averia/Orsini/software/MidiVox_Orsini/SynthEngine.ino

#include <avr/interrupt.h>
#include "SynthData.h"

// Oscillator internal variable

bool oscRunning = false;
float oscPosition = 0;
float oscSpeed = 0;
const prog_uint8_t *oscDataStart = 0;
int oscDataLen = 0;
int currentNote = 0;
float currentFrequency = 0;
float pitchBendVal = -12;
float freq = 261.6255653006f; //C3
fixed oscFCut = i2fp(1);
fixed oscFRes = 0;
fixed oscFMix = 0;
float oscLoopWidth = 1.0;
fixed ampValue=i2fp(1);
fixed fltHeight=0 ;
fixed fltSpeed=0 ;
fixed fltDelay=0 ;
fixed outValue=0 ; // output for release

// Oscillator external parameters
int oscShapeParam=0 ;
float oscFrequencyParam=0 ;

fixed clipFPlus=0 ;
fixed clipFMinus=0 ;

// Wave shape data
int oscShapeCount=6 ;

const prog_uint8_t *oscShapeTable[]= {
  sineTable,
  triTable,
  sawTable,
  squareTable,
  stairExpTable,
  particularHardTable,
};

#define DRIVER_SAMPLERATE 15625.0f

void SE_SetPitchBend(float pitchBend){                // EXPERIMENTAL
  pitchBendVal = pitchBend;
  if (oscFrequencyParam==0)  return;
  else{
    float freqFactor=(pow(2.0,(currentNote+pitchBendVal)/12.0)) ;
    currentFrequency = (freq*freqFactor);
    SE_SetFrequency(currentFrequency);
  }
};

void SE_SetFrequency(float frequency){
  if (frequency==0) {
    oscFrequencyParam=0 ;
    oscRunning=false ;
  }
  else {
    oscRunning=true ;
    oscFrequencyParam = frequency;
    oscSpeed=(frequency*oscDataLen)/DRIVER_SAMPLERATE; 
  }
};

void SE_SetNote(int note){
  currentNote=note;
  float freqFactor=(pow(2.0,(currentNote+pitchBendVal)/12.0)) ;
  //currentFrequency = freq*freqFactor;
  SE_SetFrequency(freq*freqFactor) ;
};

void updateLoopPoints() {
  // original squealer method
  //int len=oscShapeLength[oscShapeParam];
  //int o1=128;
  //int o2=0x100*oscLoopWidth ;
  //if (o1+o2>0x100) o2=0x100 ;

  oscDataStart=oscShapeTable[oscShapeParam];
  oscDataLen=0x100*oscLoopWidth;

  SE_SetFrequency(oscFrequencyParam) ;

}

void SE_SetShape(float shape) {
  int newShape=shape*oscShapeCount-0.01 ;
  if (newShape==oscShapeParam) return ;

  oscShapeParam=newShape ;
  updateLoopPoints() ;
  oscPosition=0;
};

void SE_SetWidth(float w) {
  oscLoopWidth=w;
  updateLoopPoints() ;                                  // DISABLED LOOP POINTS ... sorta
}

void SE_SetFilterCut(float cut) {
  oscFCut=fl2fp(cut*cut) ;
};

void SE_SetFilterMix(float mix) {
	
  oscFMix=fl2fp(mix) ;
};

void SE_SetOutput(float out) {
  outValue=fl2fp(out) ;
};

void SE_SetFilterRes(float res) {
  float tmpRes=(1-res) ;
  oscFRes=fl2fp(1-tmpRes*tmpRes*tmpRes) ;
};

void SynthEngine_Setup() {
  oscShapeParam=0 ;
  oscFrequencyParam=0 ;
  SE_SetNote(0) ;
  SE_SetShape(0.9) ;
  clipFPlus=i2fp(16-FIXED_SHIFT) ;
  clipFMinus=-clipFPlus ;
}

// variables for oscillators

uint16_t index = 0;          // index for wave lookup (the upper 8 bits of the accumulator)
fixed osc = 0;               // oscillator output
uint8_t rawOsc=0 ;

// ProcessSample:
// returns a unsigned 16 bit value
// to be sent to the DAC. This routine
// is called for every sample

uint16_t SynthEngine_ProcessSample() {

  // Return 0 if we don't run
  if (!oscRunning){
   return 0x8000 ;
  }
  // calculate new position inside the
  // current wavetable. 

  oscPosition +=oscSpeed ;  // add in pith, the higher the number, the faster it rolls over, the more cycles per second
  index=((int)oscPosition) ;

  if (index>=oscDataLen) {
    oscPosition-=oscDataLen ;
    index-=oscDataLen ;
  }
  
  //tempVal = oscDataStart[index];
  //uint8_t tempVal = random(0,255) / 2 ;
  
  memcpy_P(&rawOsc,&oscDataStart[index],1);
	
	//rawOsc = (rawOsc+random[rawOsc,0,255])/2;
  osc=(rawOsc-0x80)<<(FIXED_SHIFT-8+4) ;

  //ampValue -= lfoValue;
	
  //osc=fp_mul(osc,ampValue) ;				// not needed while ampvalue is 1
  fixed lpin =fp_mul(osc,FP_ONE-oscFMix) ;
  fixed hpin = -fp_mul(osc,oscFMix) ;

  //  fixed difr = fp_sub(osc,fltHeight);
  fixed difr = fp_sub(lpin,fltHeight);
  fltSpeed = fp_mul(fltSpeed,oscFRes);		//mul by res, it's some kind of inertia. caution to feedback
  fltSpeed = fp_add(fltSpeed,fp_mul(difr,oscFCut)); //mul by cutoff, less cutoff = no sound, so better not be 0.      

  fltHeight += fltSpeed ;
  fltHeight+=fltDelay-hpin ;

  osc=fltHeight ;

  if (fltHeight>clipFPlus) {
    fltHeight=clipFPlus ;
  } 
  else if (fltHeight<clipFMinus){
    fltHeight=clipFMinus ;
  }

  fltDelay=hpin;
  osc=fp_mul(osc,outValue);
  osc<<=2;
  return osc+0x8000;   // sample format for DAC is 12 bit, left justified
}
