averia/Orsini/software/MidiVox_Orsini/Fixed.h

/*

    This file is part of the Aduino Piano Squealer.

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
    Copyright 2008, 2009 Marc Nostromo	

*/

// fixed point arithmatic

#ifndef _FIXED_H
#define _FIXED_H

#include <inttypes.h>

// We use 16 signed ints

typedef int16_t fixed;

#define FIXED_SHIFT		8
#define FIXED_SCALE		(1 << FIXED_SHIFT)

#define i2fp(a)			((a) << FIXED_SHIFT)
#define fp2i(a)			((a) >> FIXED_SHIFT)

#define fp_add(a, b)	((a) + (b))
#define fp_sub(a, b)	((a) - (b))

#define FP_FRACMASK FIXED_SCALE-1 ; 

#define fp_mul(x,y)		((fixed)(((int32_t)(x) * (int32_t)(y)) >> FIXED_SHIFT))


#define FP_ONE		(1 << FIXED_SHIFT)

extern fixed fl2fp(float val);
extern float fp2fl(fixed val);

#endif/*_FIXED_H*/
