averia/Orsini/software/MidiVox_Orsini/SynthData.h

#ifndef _SYNTH_DATA_H_
#define _SYNTH_DATA_H_


#include <inttypes.h>
#include <avr/pgmspace.h>

extern const prog_uint8_t sineTable[] ;
extern const prog_uint8_t triTable[] ;
extern const prog_uint8_t sawTable[] ;
extern const prog_uint8_t squareTable[] ;
extern const prog_uint8_t stairExpTable[] ;
extern const prog_uint8_t particularHardTable[] ;
#endif
